StudioWorldTree/AICamera/openspec/changes/add-bay-glass/proposal.md

# add-bay-glass

> **ACTIVE BUILD**

## Why

The brick state is for a filmmaker. The glass is an EVF: tungsten, tally,
waveform. A little sci-fi. Dark first. Separate section.

## What

- `/bay` SvelteKit page, prerendered
- Header link Bay
- Dark-locked surface, Space Age + Tactic Extra Extended Black
- Mag rack, VRAM waveform, zram vs disk, live vs plate
- Capability: `stage-bay`

## Impact

- Capabilities: MODIFIED `stage-bay` (glass)
- ADRs: none

## User journey & surfaces

From any notebook page, Bay in the header. Working / empty / failed / off
as in `add-stage-bay`.

## Out of scope

- Light theme for `/bay`
- Editing models from the glass
