StudioWorldTree/AICamera/openspec/changes/archive/2026-09-10-add-datasheet-pack/proposal.md

# add-datasheet-pack

> **ACTIVE BUILD**

## Why

CAD and buys need envelopes and URLs, not folklore.

## What

- Manifest under `docs/references/`
- Thor series DS already in tree
- List still-wanted PDFs
- Capability: `hardware-kit`

## Impact

- Capabilities: ADDED datasheet pack
- ADRs: none

## User journey & surfaces

No new UI because this is a document pack.

## Out of scope

- Camera SKU PDFs until we pick them
