StudioWorldTree/AICamera/openspec/changes/archive/2026-09-10-add-thor-enclosure/proposal.md

# add-thor-enclosure

> **ACTIVE BUILD**

## Why

The body camera mounts to the Thor box. First article is a resin
fit-check on the Anycubic, not a production housing.

## What

- Wrap the AGX kit envelope first (243.19 × 112.40 × 56.88 mm)
- Body-cam mount + TTP vents
- STL when Blender MCP is connected
- Capability: `hardware-kit`

## Impact

- Capabilities: ADDED enclosure
- ADRs: none

## User journey & surfaces

No new UI because this is CAD and a print.

## Out of scope

- Production SOM lid (87 × 100 × 15.29 mm) until the kit print fits
- Blender work until MCP is connected this session
