StudioWorldTree/AICamera/openspec/changes/add-bay-feed/tasks.md

# Tasks

- [x] snapshot.py on fractal1
- [x] serve.py bound to 100.103.147.70:8745
- [x] systemd enable
- [x] last-plate.json committed from a live snapshot
- [x] vite proxy `/bay-api`
