StudioWorldTree/AICamera/openspec/changes/add-bay-glass/tasks.md

# Tasks

- [x] `/bay` route + Header link
- [x] HUD typefaces loaded
- [x] Waveform, mag rack, swap split, tally
- [x] Last plate fallback
- [x] Dark-locked even when site theme is light
