StudioWorldTree/AICamera/openspec/changes/archive/2026-09-10-add-thor-carrier/tasks.md

# Tasks

- [x] Write `docs/CARRIER.md`
- [x] Delta `hardware-kit` carrier requirements
- [x] Make the T4000 HV/MV rail contract and absence of `SYS_VIN_SV` normative in the carrier delta
- [x] Add the normative T4000-default/T5000-escape criterion tied to validated hybrid encode load
