StudioWorldTree/AICamera/openspec/changes/archive/2026-09-10-add-thor-enclosure/tasks.md

# Tasks

- [x] Write `docs/ENCLOSURE.md` print notes
- [x] Blender model + STL (`docs/cad/agx_shell_front.stl`, `agx_shell_rear.stl`)
- [x] Delta `hardware-kit` enclosure requirement
