StudioWorldTree/AICamera/openspec/changes/archive/2026-09-10-add-lens-metadata/tasks.md

# Tasks

- [x] Write `docs/LENS.md`
- [x] Point record path and sensors at /i
- [x] Delta `hardware-kit` lens-metadata requirement
