StudioWorldTree/AICamera/openspec/changes/archive/2026-09-10-add-power-thermal/tasks.md

# Tasks

- [x] Write `docs/POWER.md`
- [x] Delta `hardware-kit` power requirements
