StudioWorldTree/AICamera/openspec/changes/archive/2026-09-10-add-power-thermal/reviews/2026-09-01-advise.md

# advise add-power-thermal

> **ADVISE:** accept-with-nits

**Verdict.** Split PSUs, 70/90 W T4000, resin is not a heat sink.
Steelman against: one PoE++ injector for Thor+cams — backfeed risk.
Tradeoff: no sun-load measurement without the thermal guide.

**Nits.** TDG-12271-001 absent. Same-session author+reader.

**Solid.** Drop-AI-never-record already decided; rails match the DS.
