StudioWorldTree/AICamera/openspec/changes/archive/2026-09-10-add-sensor-lens-kit/reviews/2026-09-01-advise.md

# advise add-sensor-lens-kit

> **ADVISE:** accept-with-nits

**Verdict.** 1 body CSI + 2 PoE H.265 sats, electronic iris/focus.
Steelman against: six cinema bodies — wrong spend before a print.
Tradeoff: no SKUs yet; classes only.

**Nits.** Candidate shopping list is empty of part numbers. Same-session
author+reader.

**Solid.** Count and fabric match STREAM-BUDGET bring-up.
