StudioWorldTree/AICamera/openspec/changes/archive/2026-09-10-add-datasheet-pack/tasks.md

# Tasks

- [x] Ingest DS-11945-001 v1.4
- [x] Keep `docs/references/README.md` as the manifest
- [x] Delta `hardware-kit` datasheet requirement
